ARSFI/HFSimulator/doc/QEX/attachments/Fig 1. Detailed block diagram of the IONOS Simulator.png

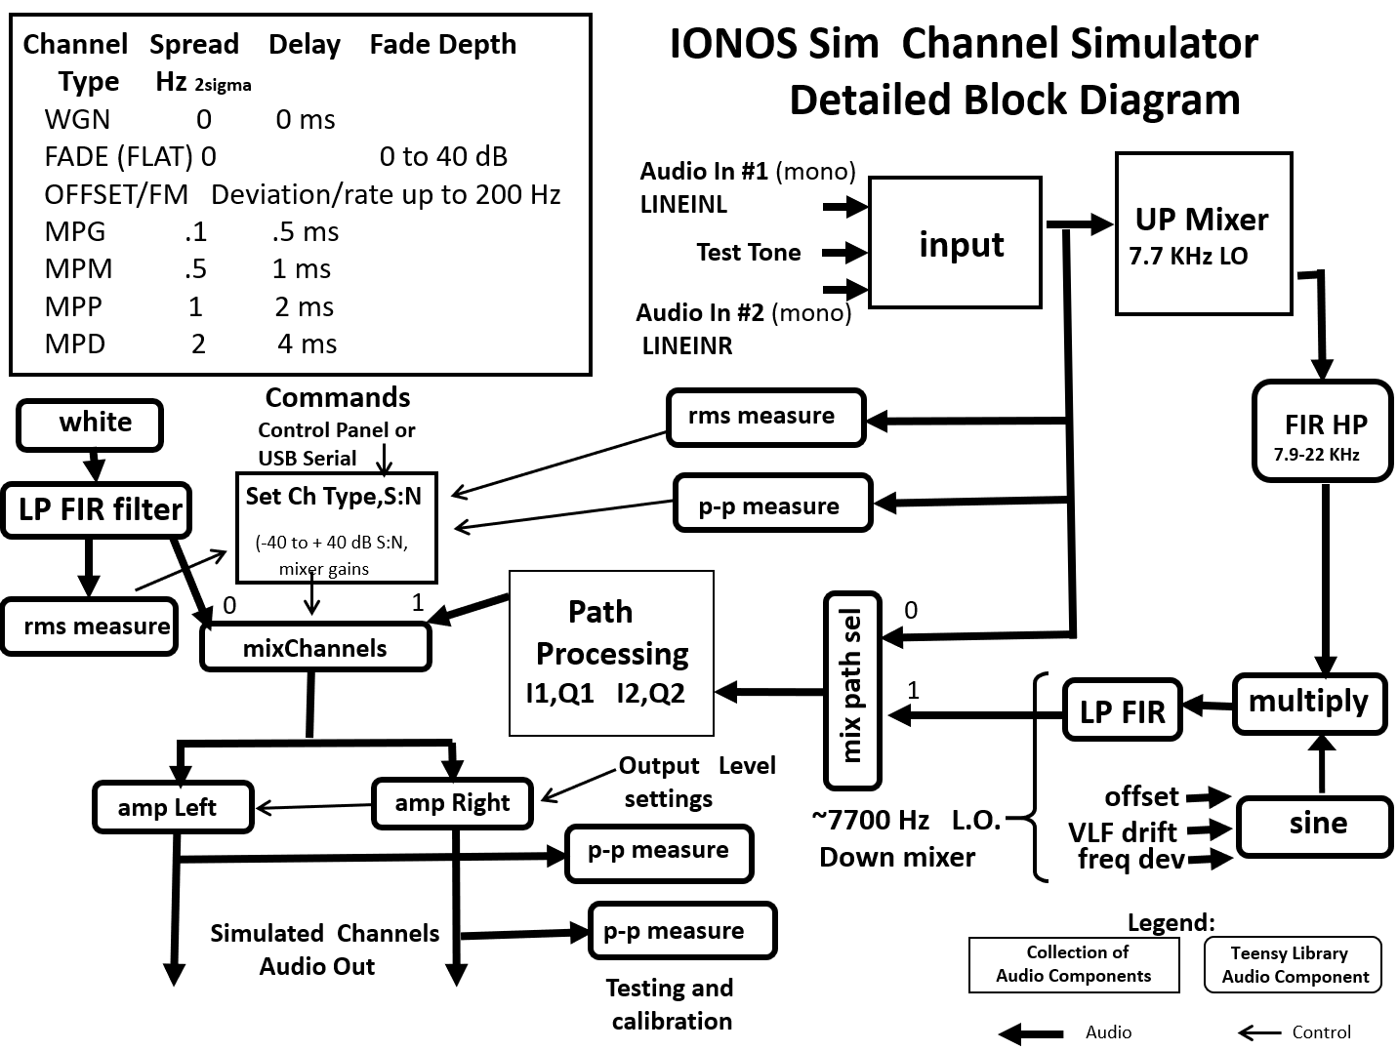
doc/QEX/attachments/Fig 1. Detailed block diagram of the IONOS Simulator.png
