ARSFI/HFSimulator/doc/QEX/attachments/Fig 3 Teensy 4.0 Processor and Audio Shield.png

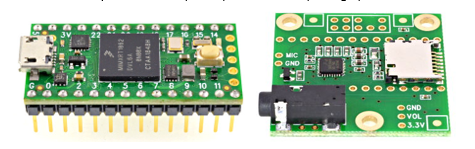
doc/QEX/attachments/Fig 3 Teensy 4.0 Processor and Audio Shield.png
