ARSFI/HFSimulator/doc/QEX/attachments/Fig 4 Photo of Rev 2 prototype PCB.png

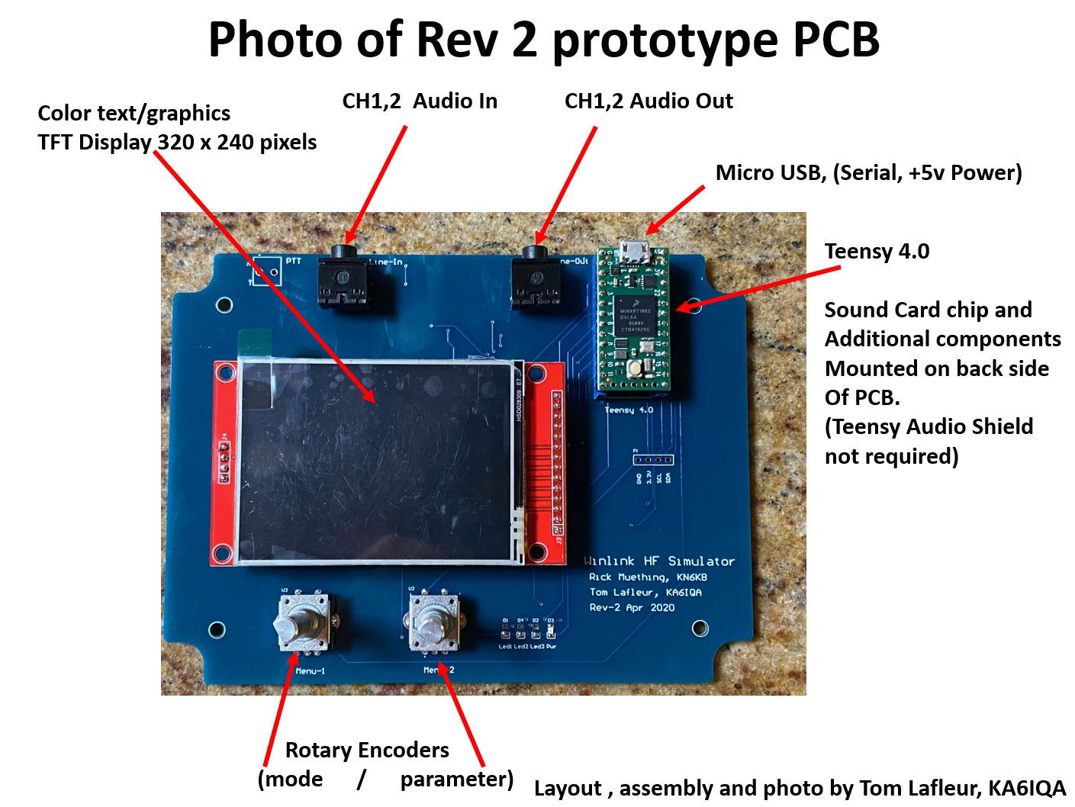
doc/QEX/attachments/Fig 4 Photo of Rev 2 prototype PCB.png
