ARSFI/HFSimulator/doc/QEX/attachments/Fig 8 Photo of First prototype production run with enclosure.png

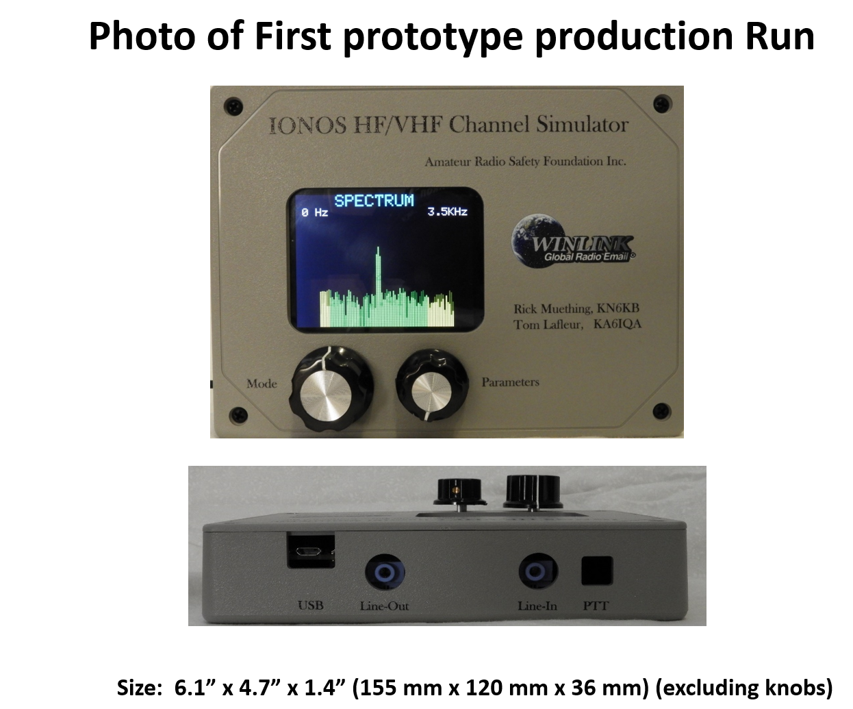
doc/QEX/attachments/Fig 8 Photo of First prototype production run with enclosure.png
