ARSFI/HFSimulator/doc/QEX/attachments/Fig 9 Gaussian 9 pole LP FIR Filter.png

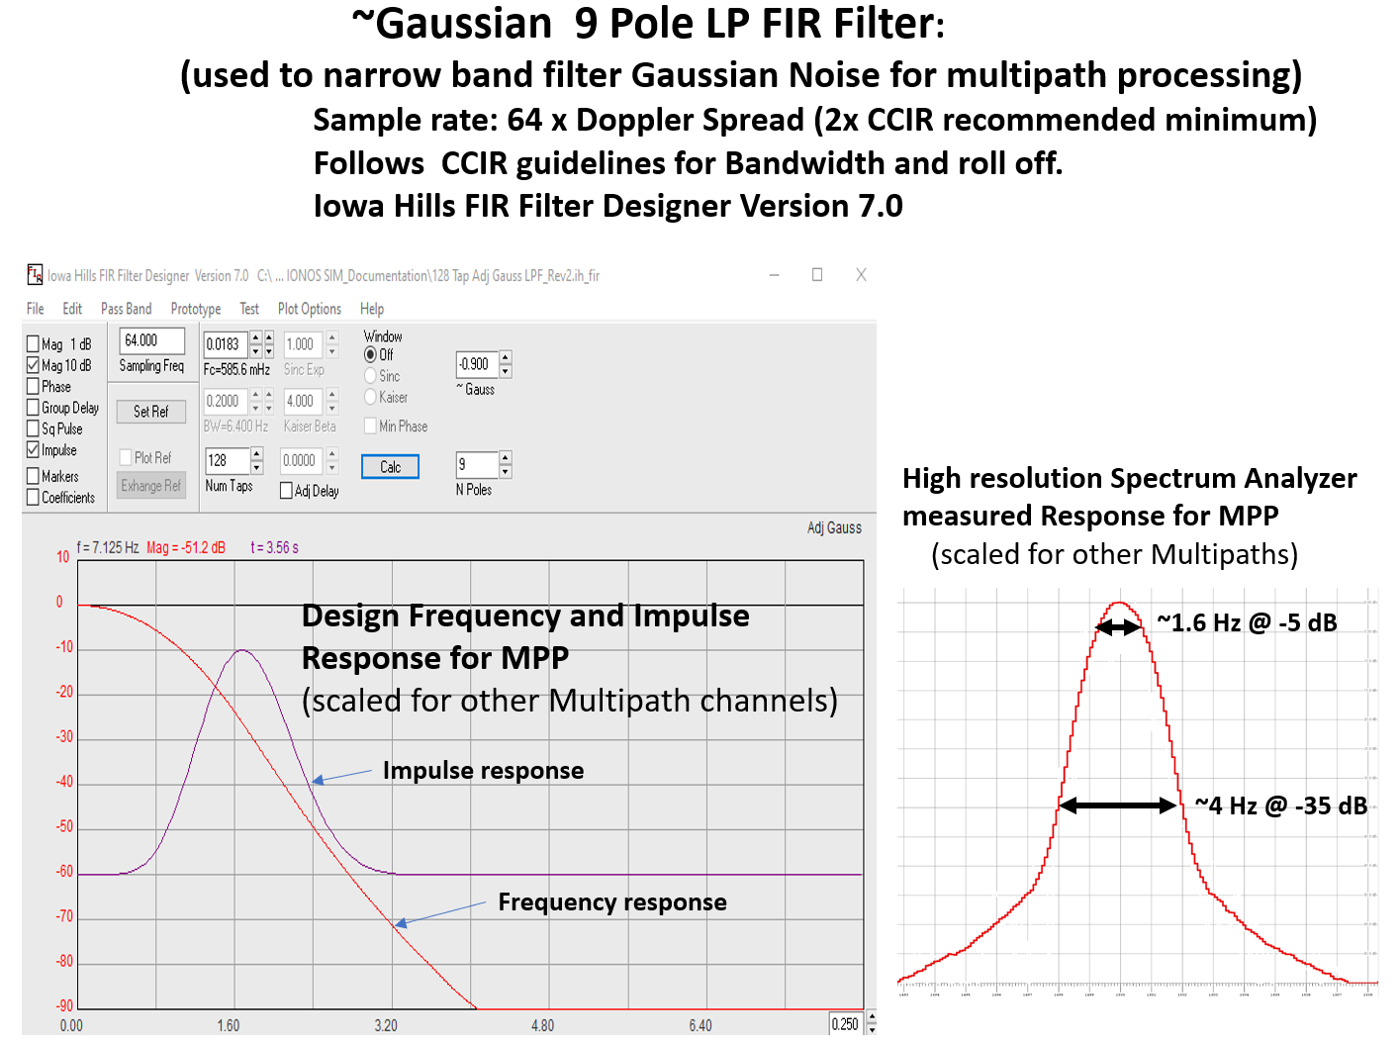
doc/QEX/attachments/Fig 9 Gaussian 9 pole LP FIR Filter.png
