ARSFI/HFSimulator/doc/QEX/attachments/Fig 10 Modem Connections to the IONOS Simulator for Half Duplex ARQ modeling.png

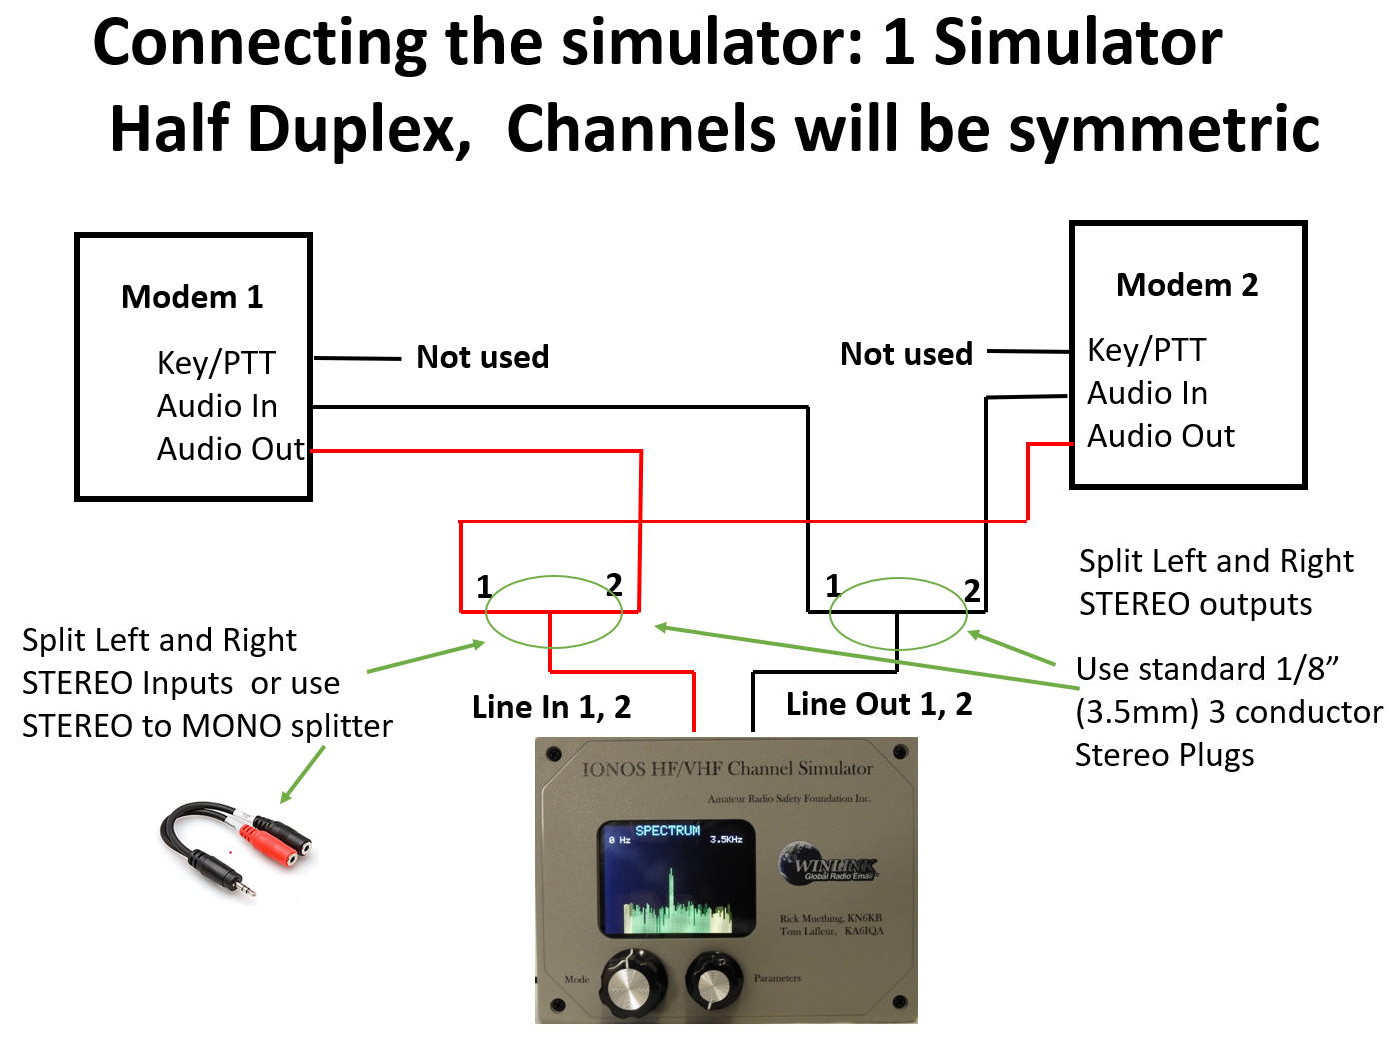
doc/QEX/attachments/Fig 10 Modem Connections to the IONOS Simulator for Half Duplex ARQ modeling.png
