ARSFI/HFSimulator/photos/IMG_9686.jpg

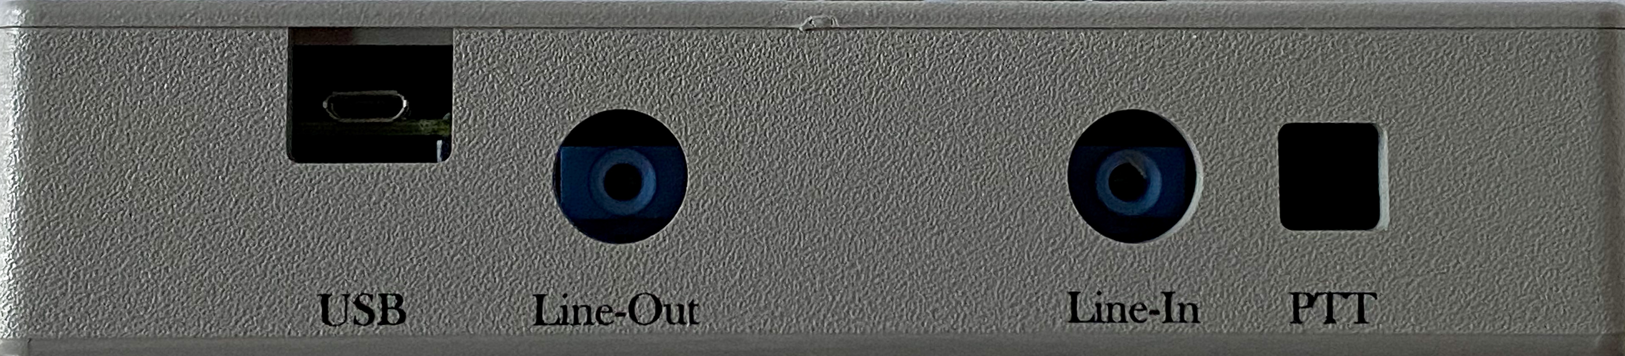
photos/IMG_9686.jpg
