ARSFI/HFSimulator/photos/IMG_9697.jpg

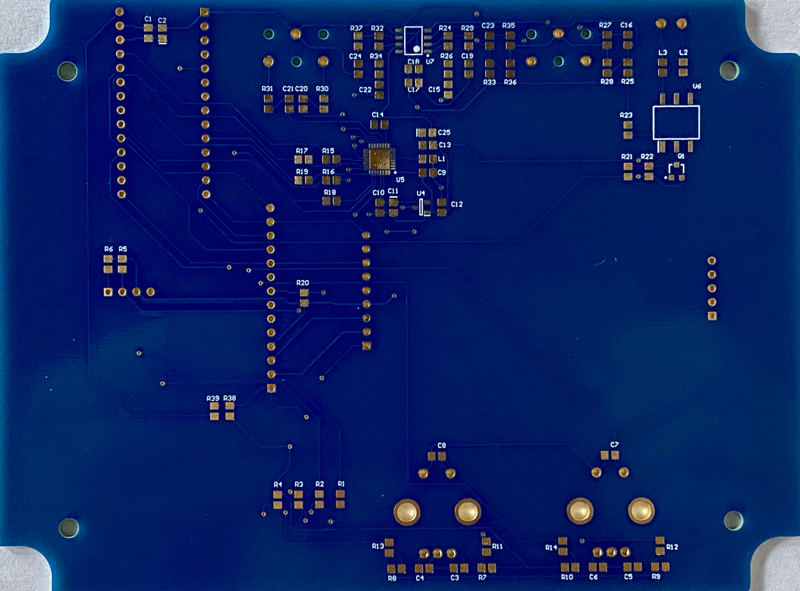
photos/IMG_9697.jpg
