ARSFI/HFSimulator/photos/IMG_9700.jpg

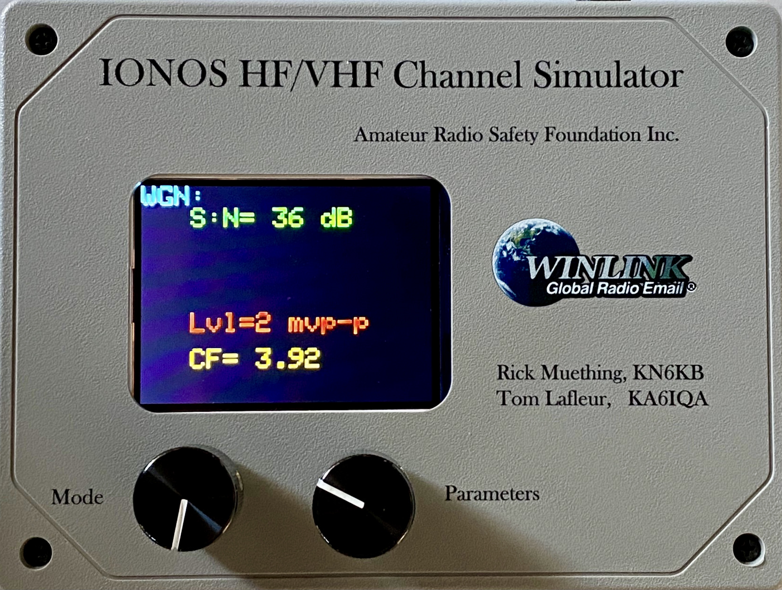
photos/IMG_9700.jpg
