ARSFI/HFSimulator/photos/IMG_9702.jpg

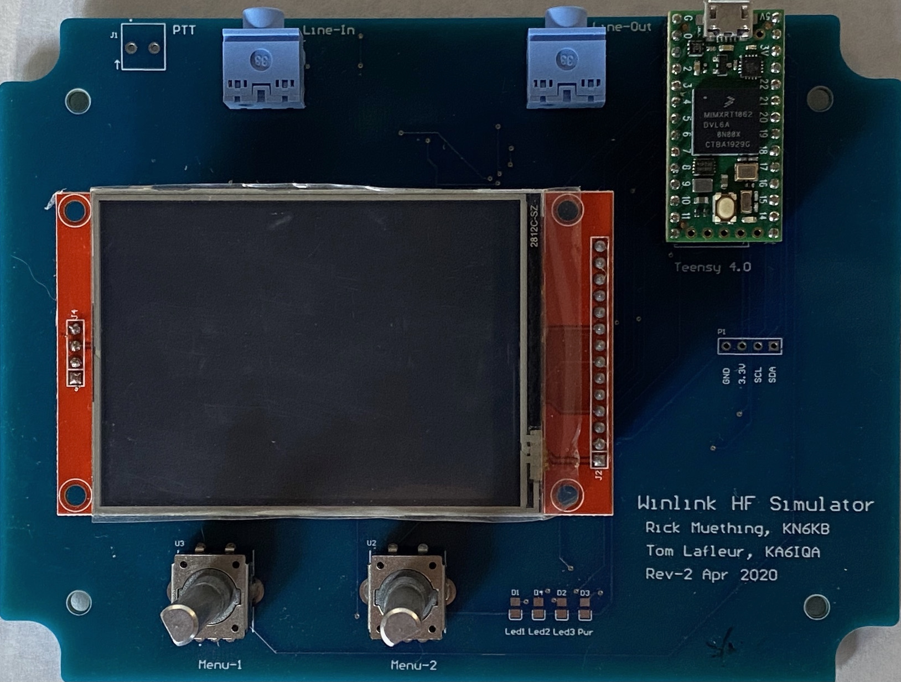
photos/IMG_9702.jpg
