ARSFI/HFSimulator/photos/IMG_9705.jpg

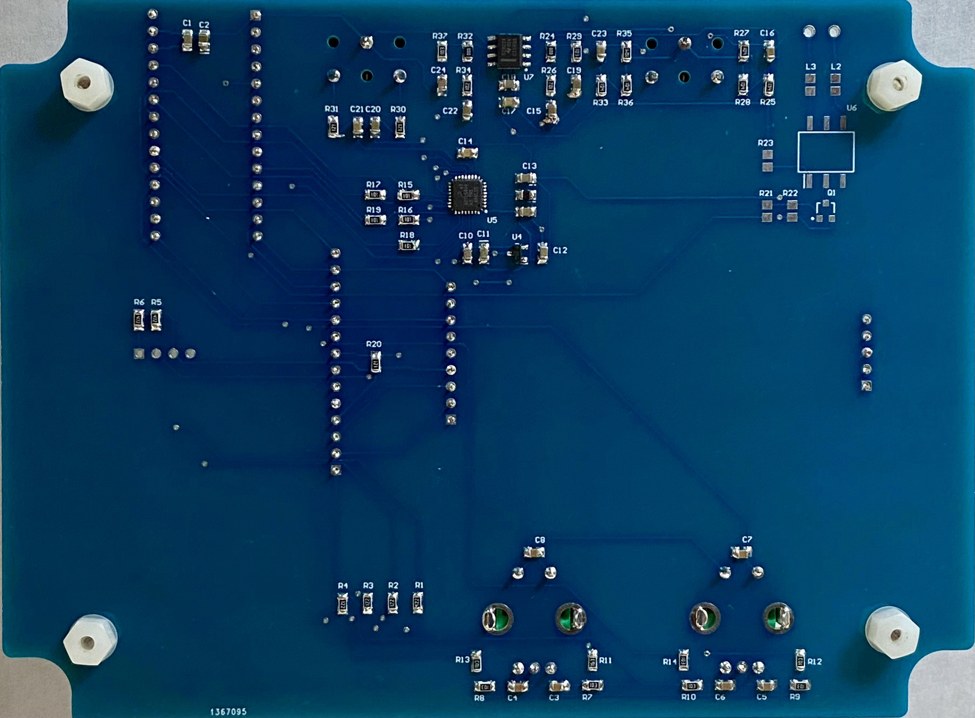
photos/IMG_9705.jpg
