ARSFI/HFSimulator/photos/IMG_9708.jpg

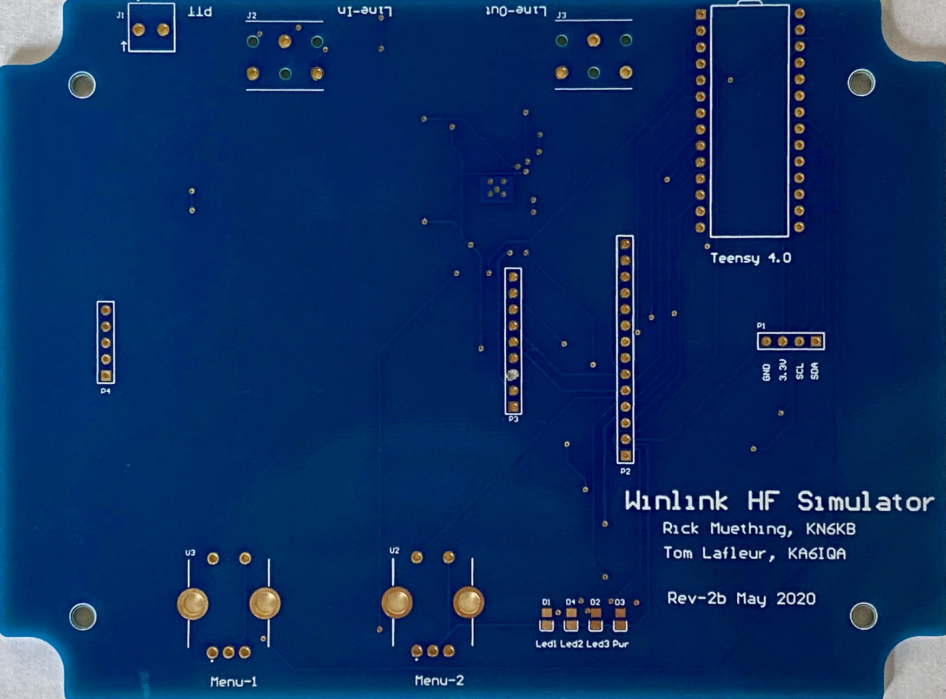
photos/IMG_9708.jpg
