ARSFI/HFSimulator/doc/QEX/attachments/Fig 11 Performance verses S_N for 5 ARQ Protocols White Gaussian Noise.png

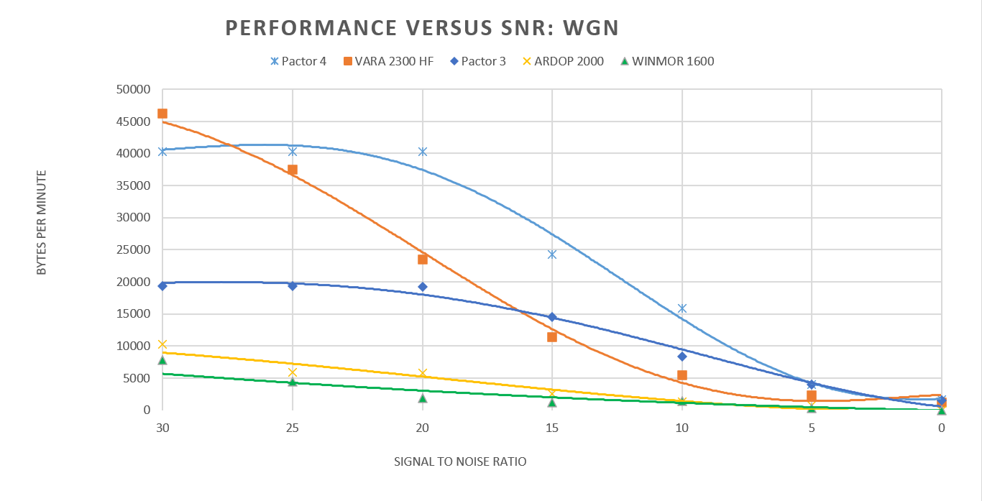
doc/QEX/attachments/Fig 11 Performance verses S_N for 5 ARQ Protocols White Gaussian Noise.png
