ARSFI/HFSimulator/doc/QEX/attachments/Fig 13 Performance verses S_N for 5 ARQ Protocols Multipath Poor MPP.png

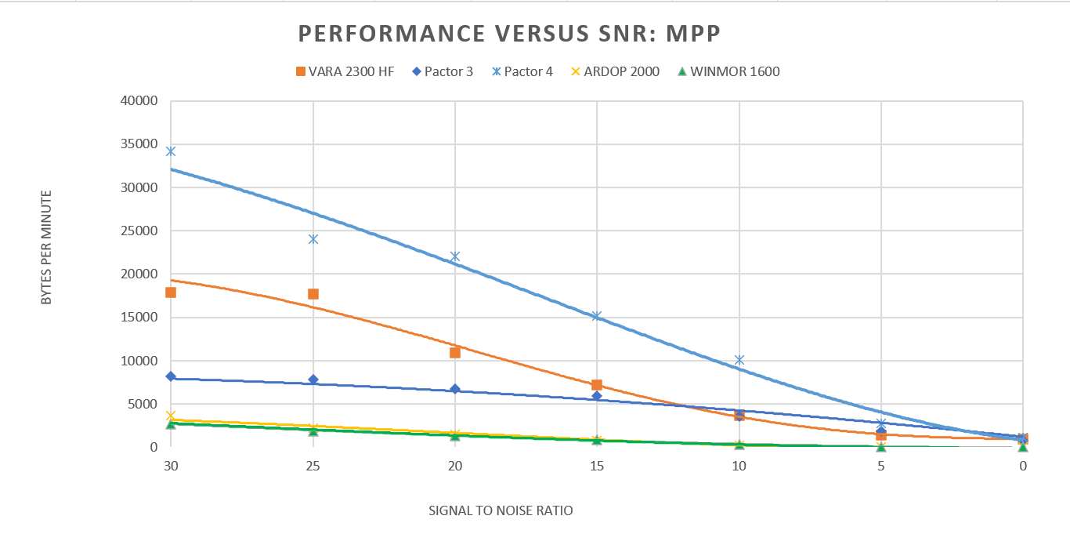
doc/QEX/attachments/Fig 13 Performance verses S_N for 5 ARQ Protocols Multipath Poor MPP.png
