ARSFI/HFSimulator/doc/QEX/attachments/Fig 14 Performance for VARA FM and AX.25_FX.25 Packet.png

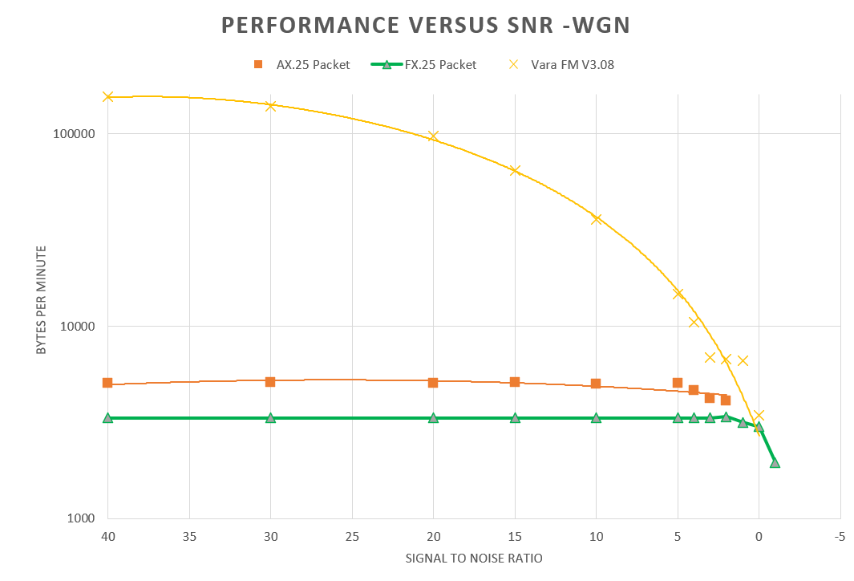
doc/QEX/attachments/Fig 14 Performance for VARA FM and AX.25_FX.25 Packet.png
