ARSFI/HFSimulator/hardware/Ver 2/sch/HF-Simulator Rev-2b.pdf

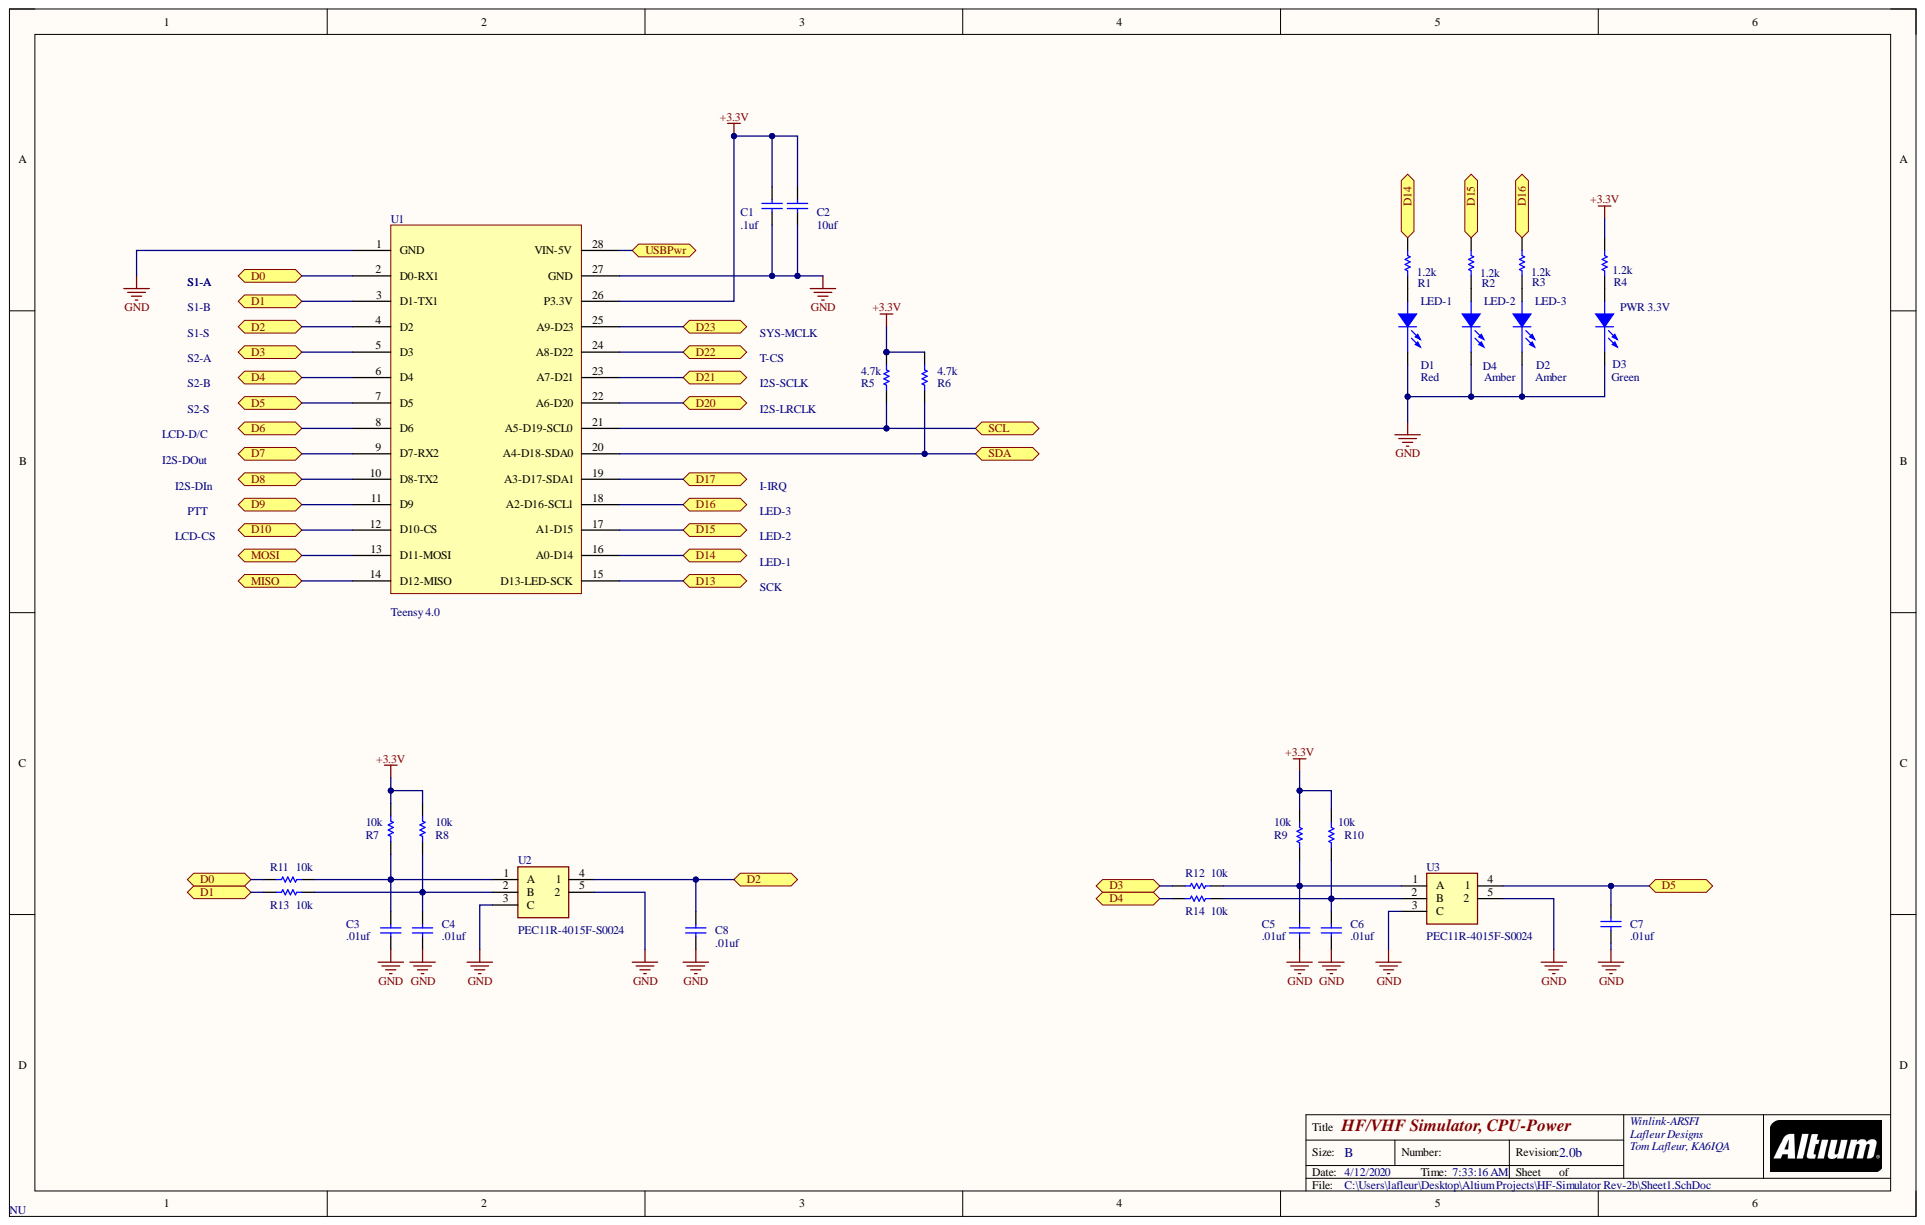
[picture p107: page 1]

Title HF/VHF Simulator, CPU-Power | Winlink-ARSFI Lafleur Designs Tom Lafleur, KA6IQA

Size: B | Number: | Revision: 2.0b
Date: 4/12/2020 Time: 7:33:16 AM | | Sheet of

C:\Users\lafleur\Desktop\AltiumProjects\HF-Simulator Rev-2b\Sheet1.SchDoc

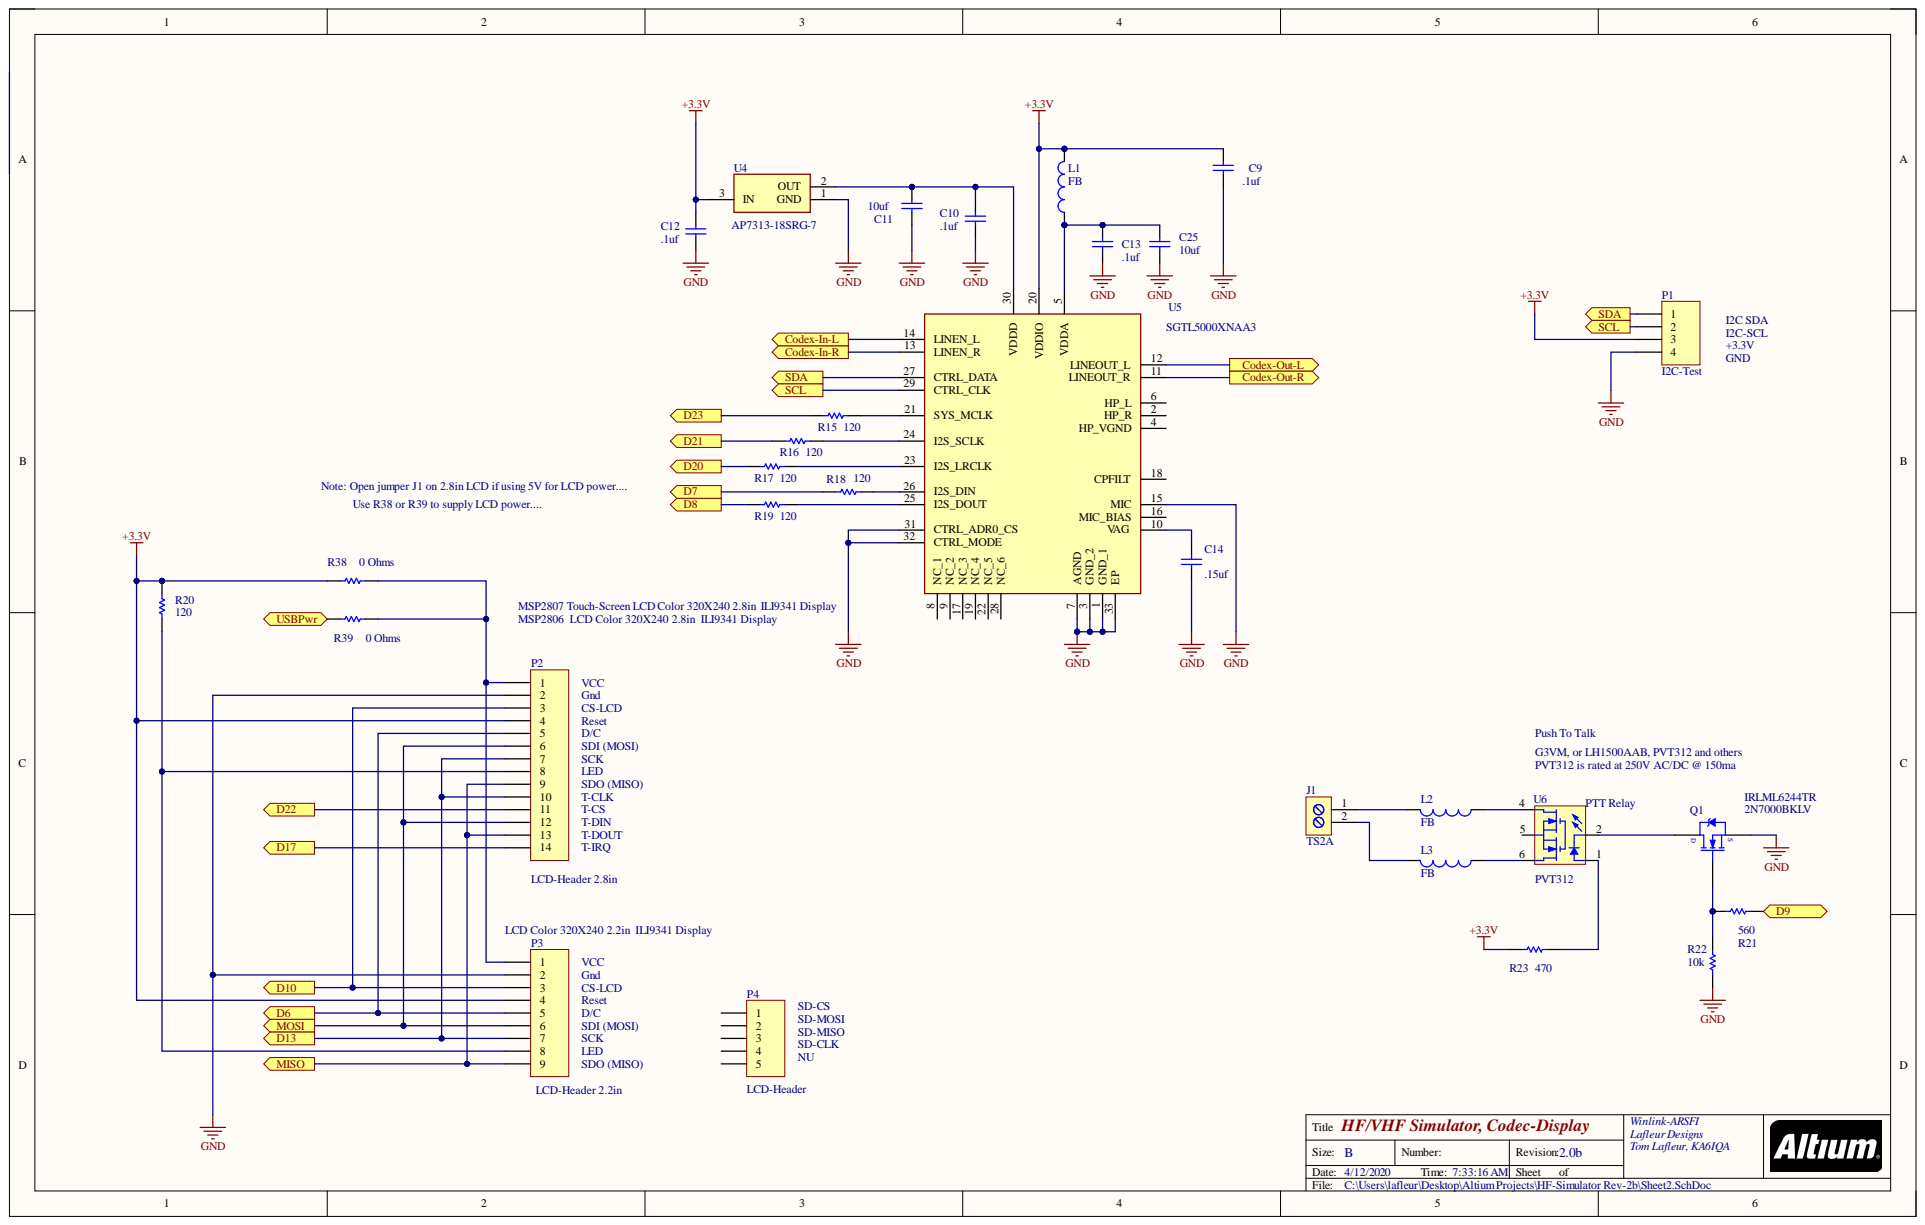
[picture p108: page 2]

Note: Open jumper J1 on 2.8in LCD if using 5V for LCD power....
Use R38 or R39 to supply LCD power....

R38 0 Ohms

MSP2807 Touch-Screen LCD Color 320X240 2.8in ILI9341 Display
MSP2806 LCD Color 320X240 2.8in ILI9341 Display

R39 0 Ohms

Push To Talk
G3VM, or LH1500AAB, PVT312 and others
PVT312 is rated at 250V AC/DC @ 150ma

HF/VHF Simulator, Codec-Display
Title

C:\Users\lafleur\Desktop\AltiumProjects\HF-Simulator Rev-2b\Sheet2.SchDoc

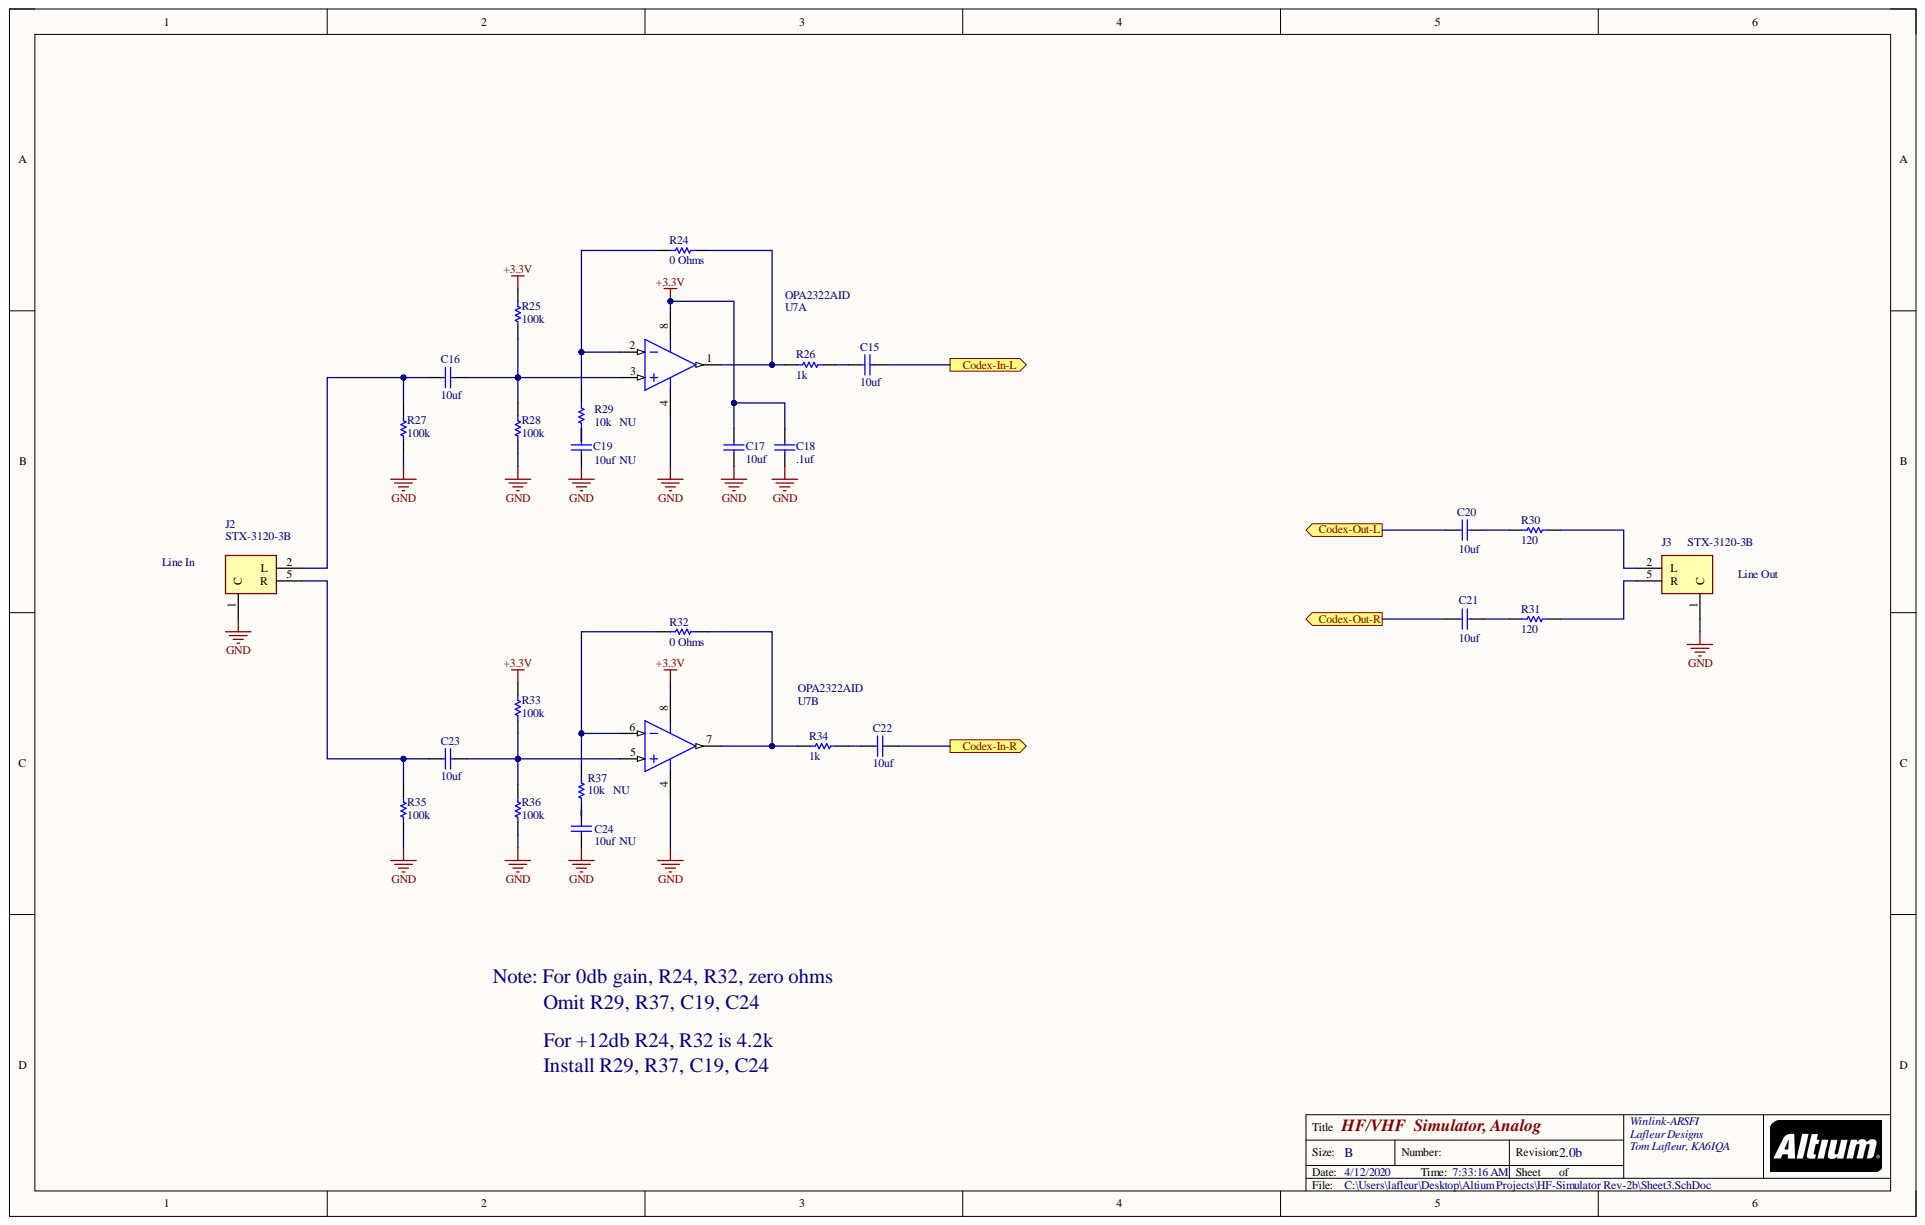
[picture p109: page 3]

Ti tl e HF/VHF Simulato r, Analo g | Winl ink-ARSFI Lafleur Des igns Tom Lafleur, KA6I QA

Si z e : B | N umber : | Revi s i on: 2 . 0 b
Dat e : 4/12/ 20 20 Ti me: 7:33:16 AM | | Sheet of

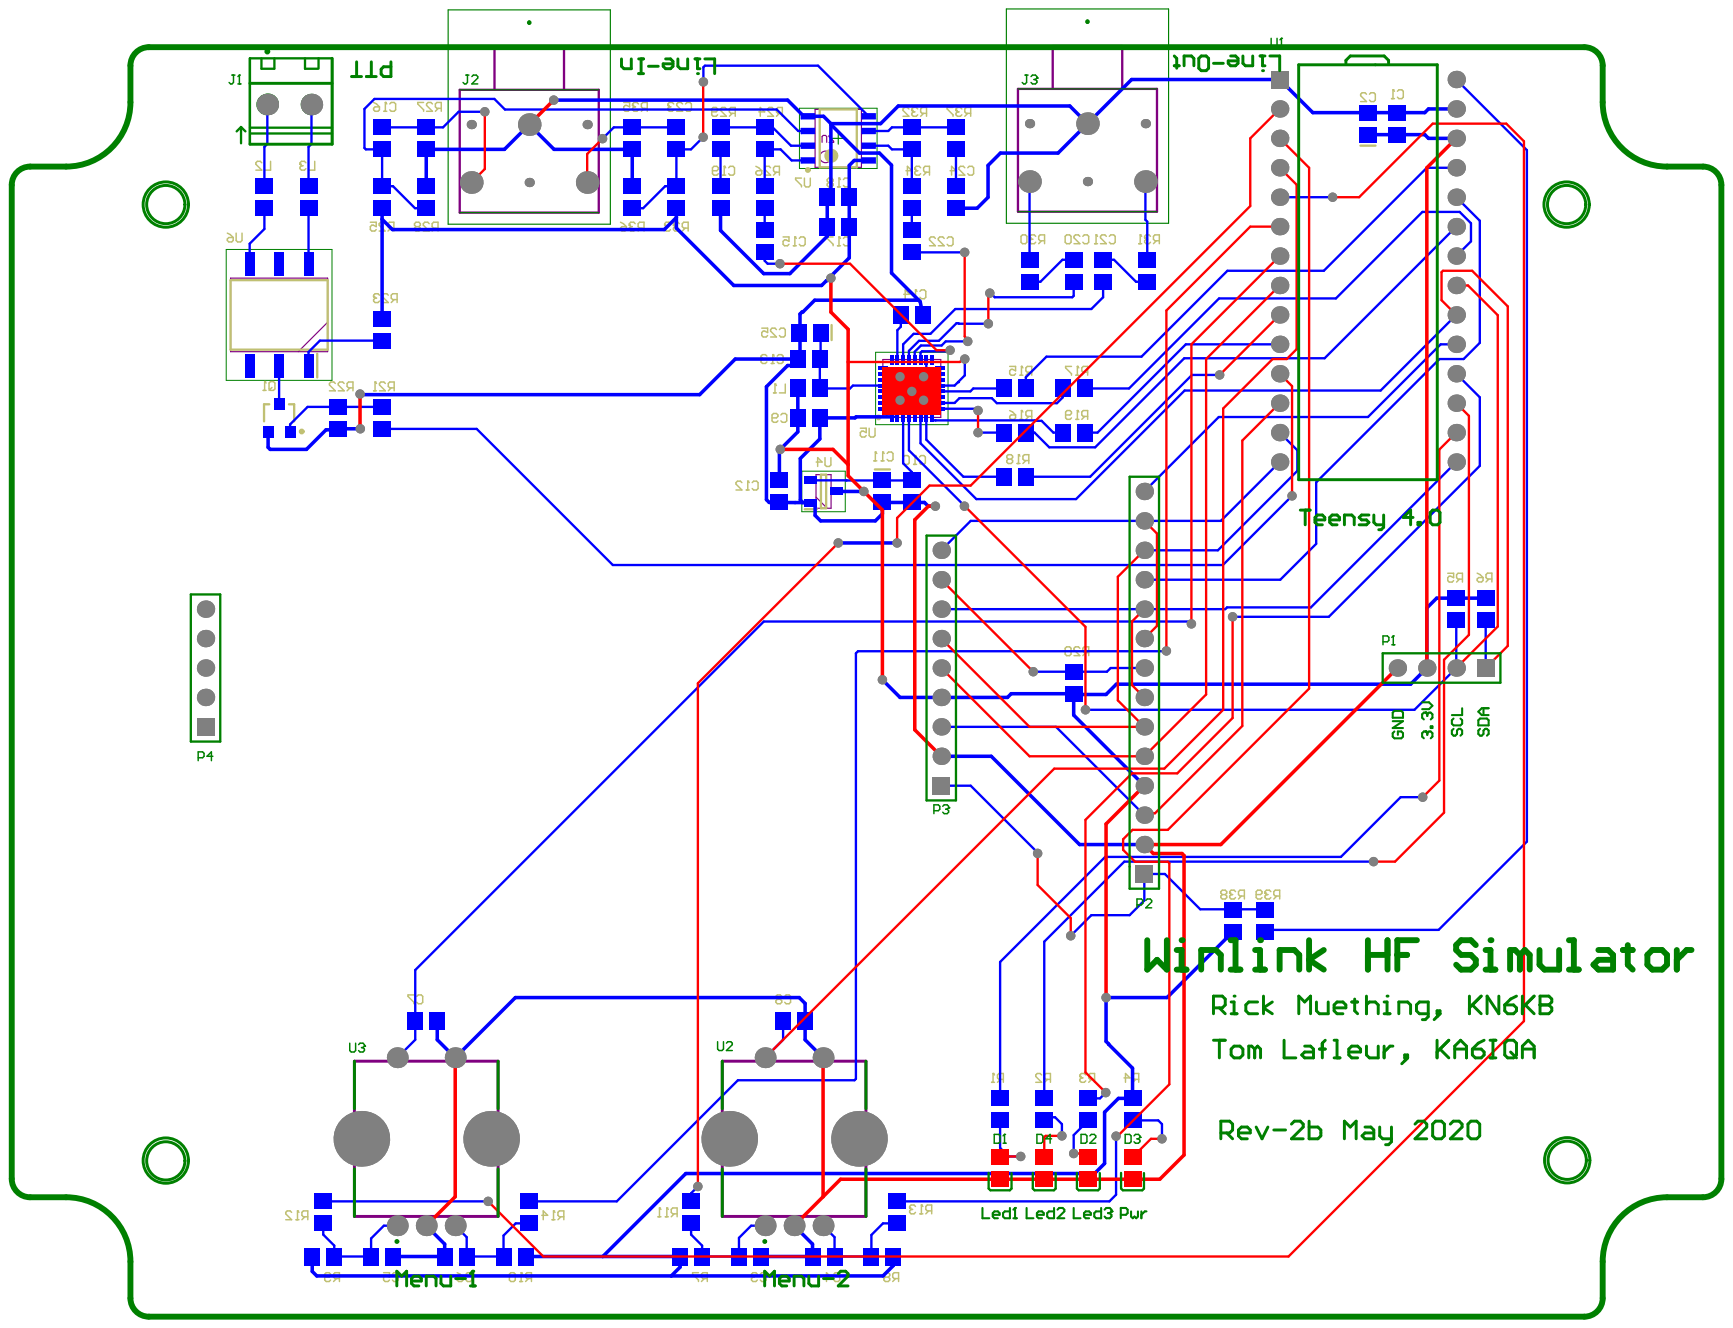
[picture p110: page 4]
