ARSFI/HFSimulator/hardware/Ver 2/sch/IONOS Simulator Schematic Sheet1.pdf

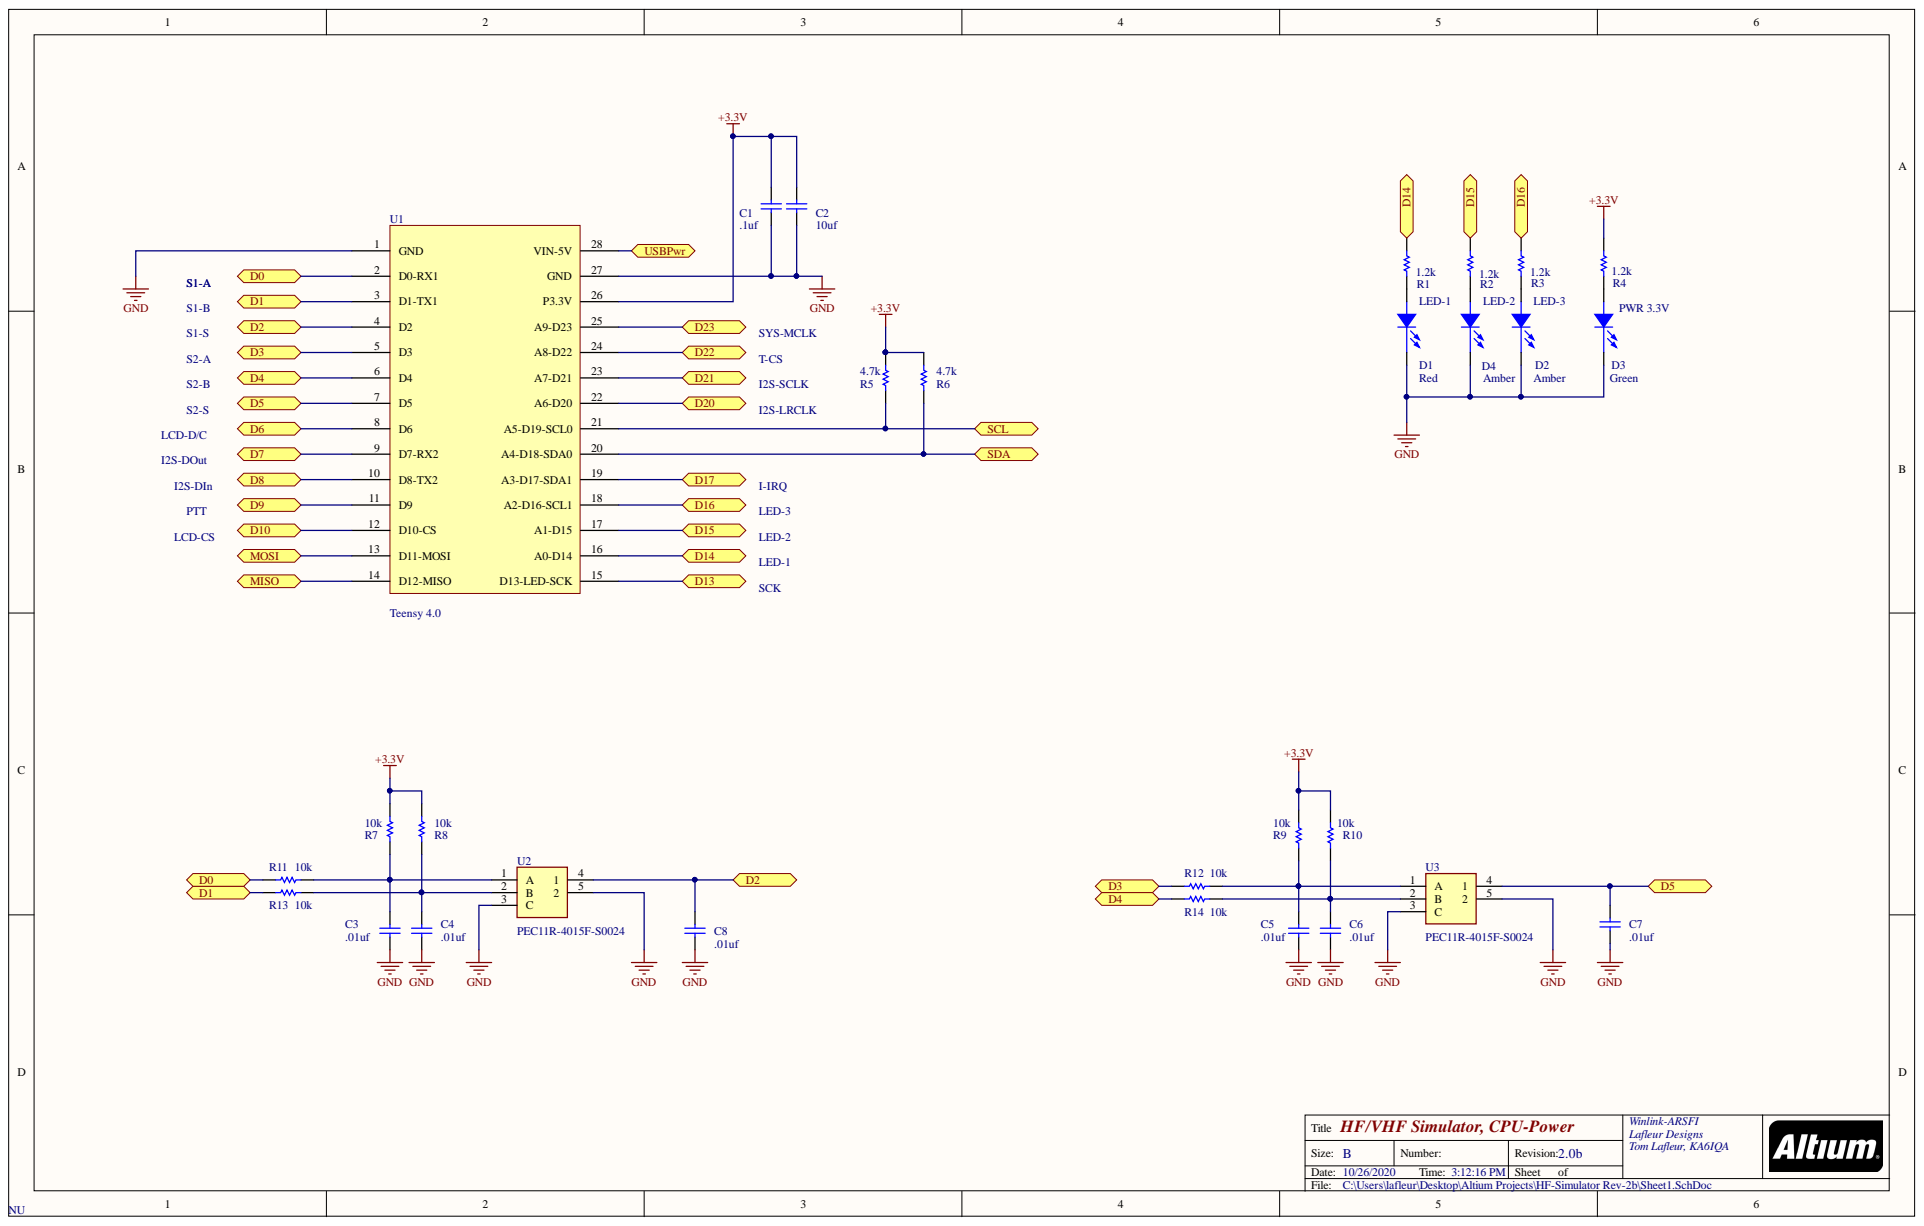
[picture p111: page 1]

HF/VHF Simulator, CPU-Power Title | Winlink-ARSFI Lafleur Designs Tom Lafleur, KA6IQA

Size: B | Number: | Revision: 2.0b
Date: 10/26/2020 Time: 3:12:16 PM | | Sheet of
File: C:\Users\lafleur\Desktop\Altium Projects\HF-Simulator Rev-2b\Sheet1.SchDoc
