ARSFI/HFSimulator/hardware/Ver 2/sch/IONOS Simulator Schematic Sheet3.pdf

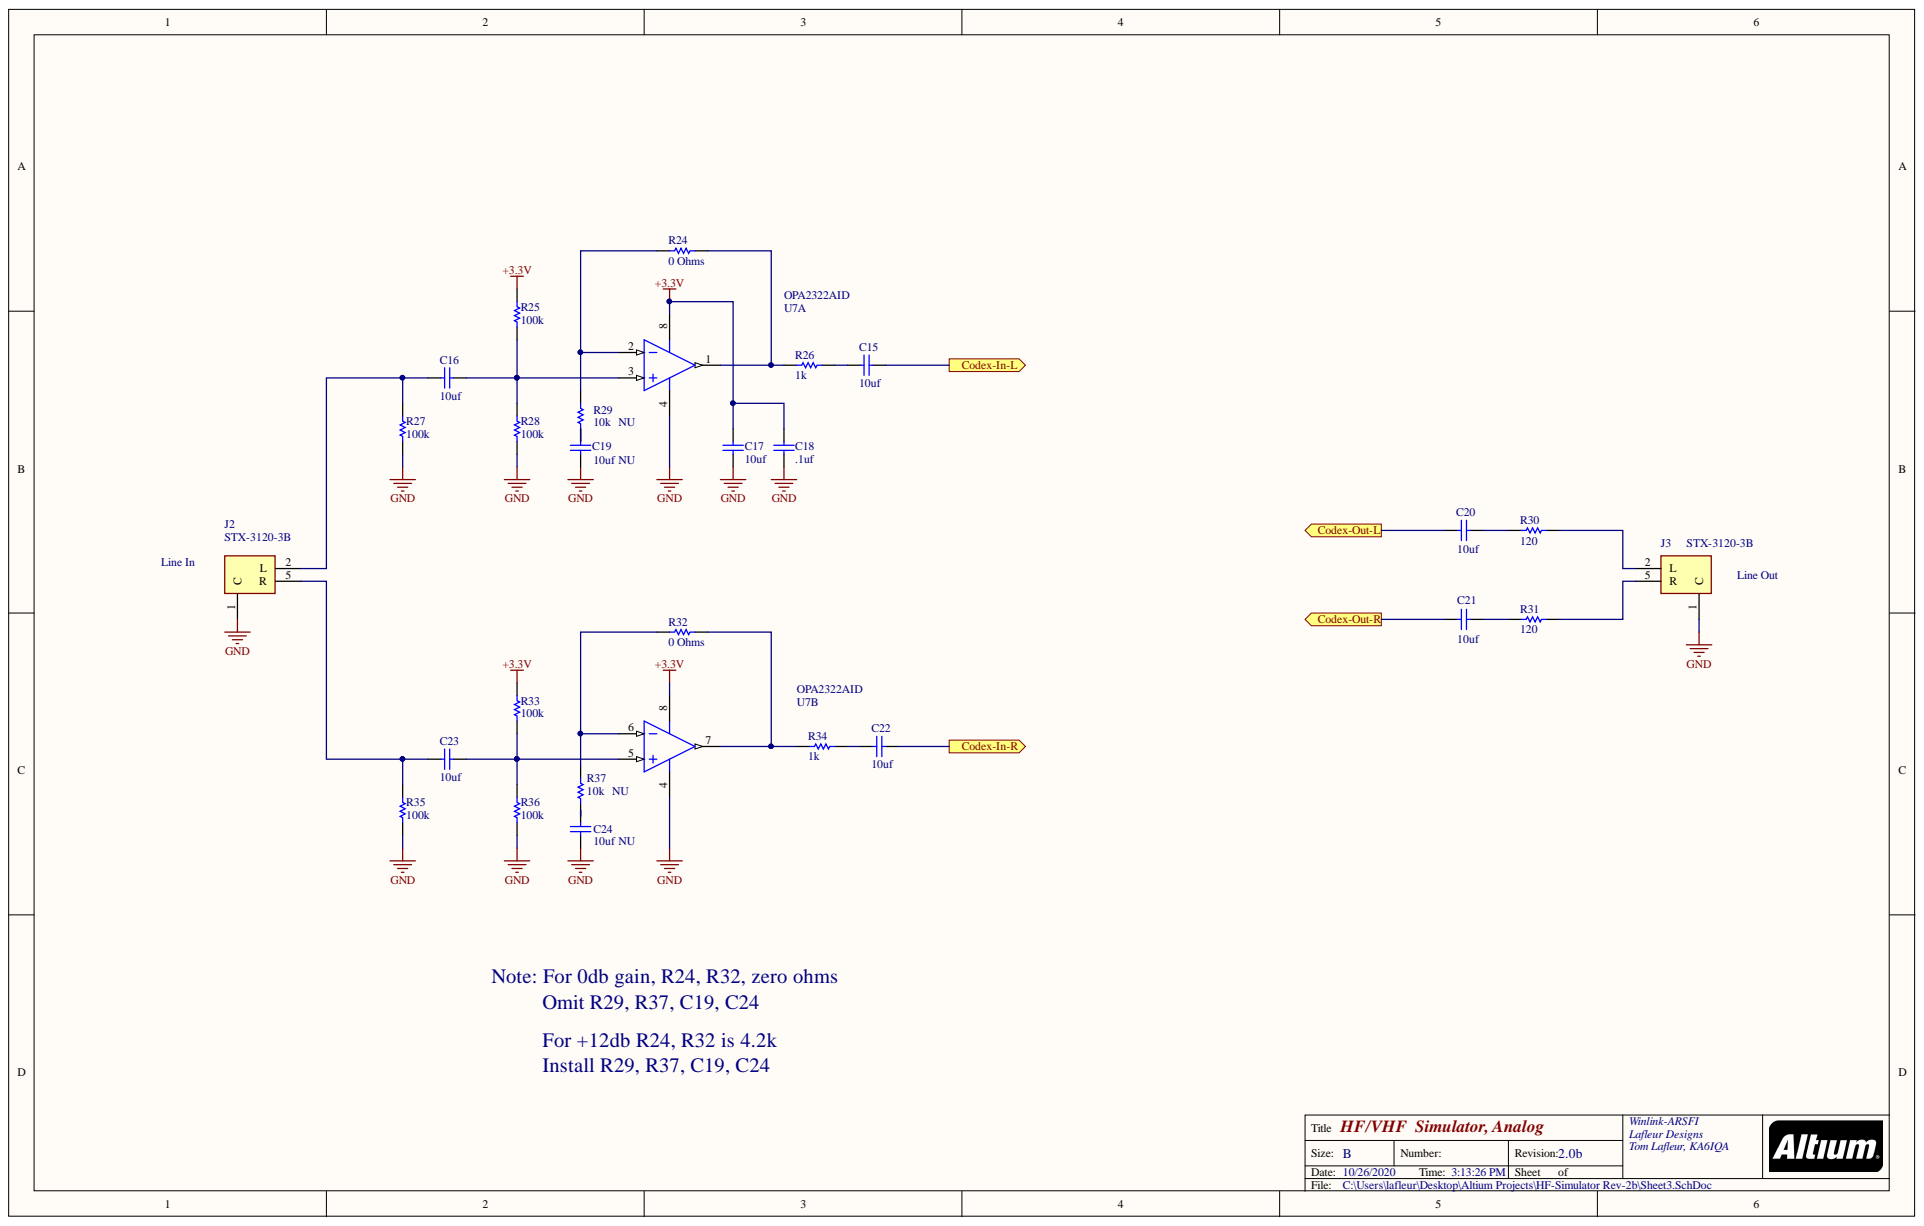
[picture p112: page 1]

HF/VHF Simulato r, Analo g Ti tl e | Winl ink-A RSFI Lafleur Des igns Tom Lafleur, KA6I QA

Size: B | Number : | Revi s ion: 2 . 0 b
Date: Ti me: | | Sheet of
Fi le: s \HF-Si mulator Rev-2b\Sheet3.SchDoc
