ARSFI/HFSimulator/hardware/Ver 3/case/PolyCase Ver-3/HF-Sim PolyCase V3/Rev-2/DC-45PMBYT_ASS'Y_BOX _BodyDrawing v1.pdf

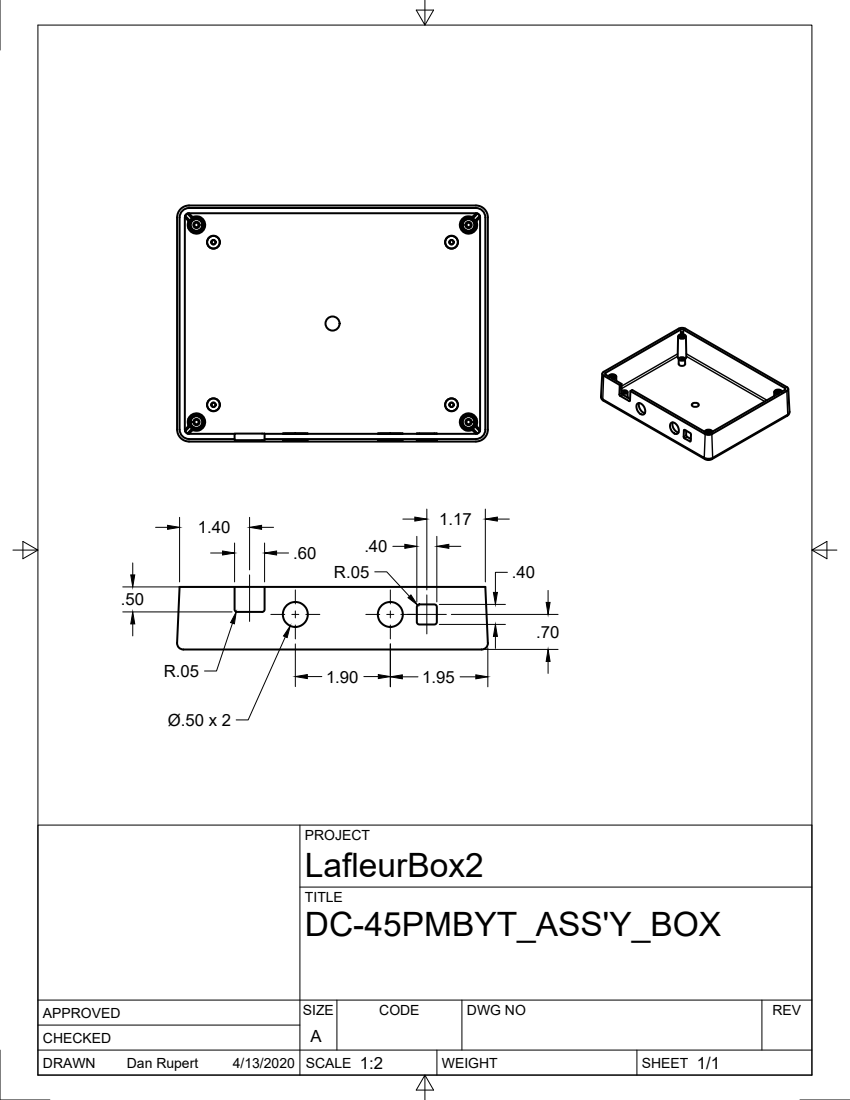
[picture p113: page 1]
SIZE; CODE; DWG NO; REV; Dan Rupert
