ARSFI/HFSimulator/hardware/Ver 3/case/PolyCase Ver-3/HF-Sim PolyCase V3/Rev-2/DC-45PMBYT_ASS'Y_BOX Drawing LID v1.pdf

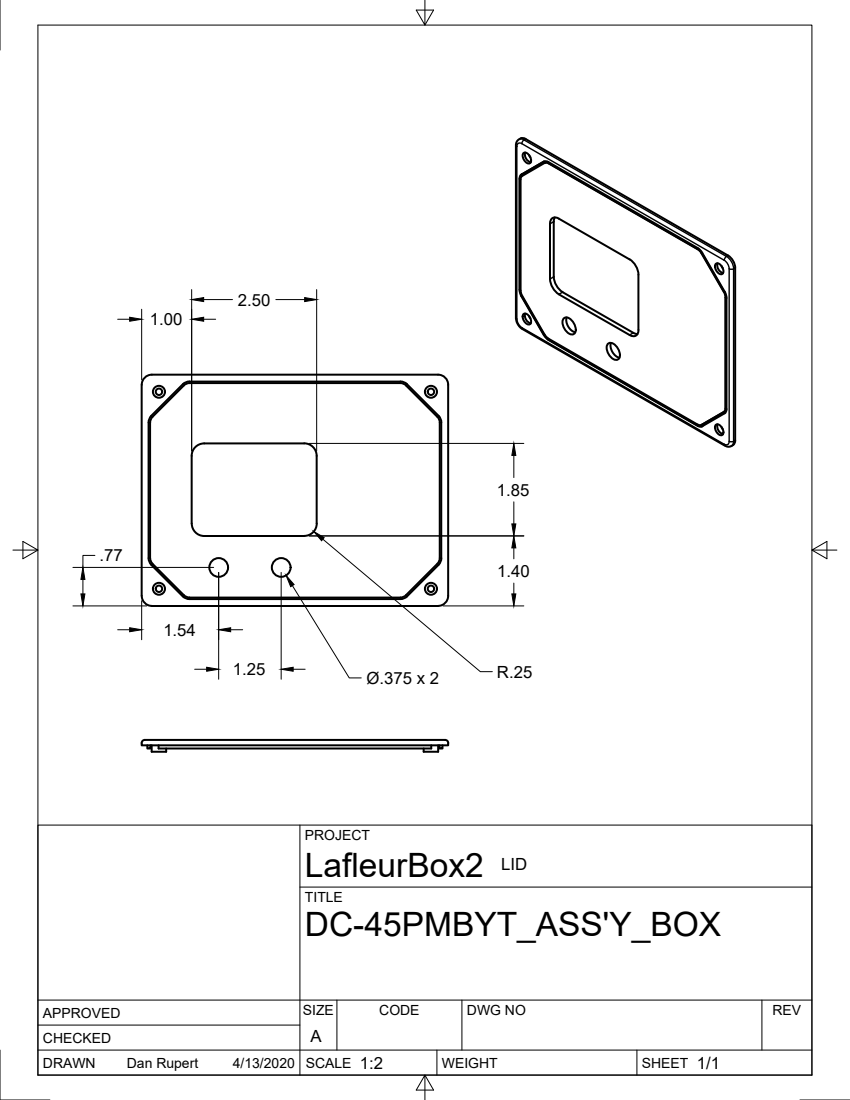
[picture p114: page 1]
SIZE; CODE; DWG NO; REV; Dan Rupert
