ARSFI/HFSimulator/hardware/Ver 3/case/PolyCase Ver-3/HF-Sim PolyCase V3/Rev-1/Lafleur_DC-45PMBYT_ASS'Y Drawing v1 LID.pdf

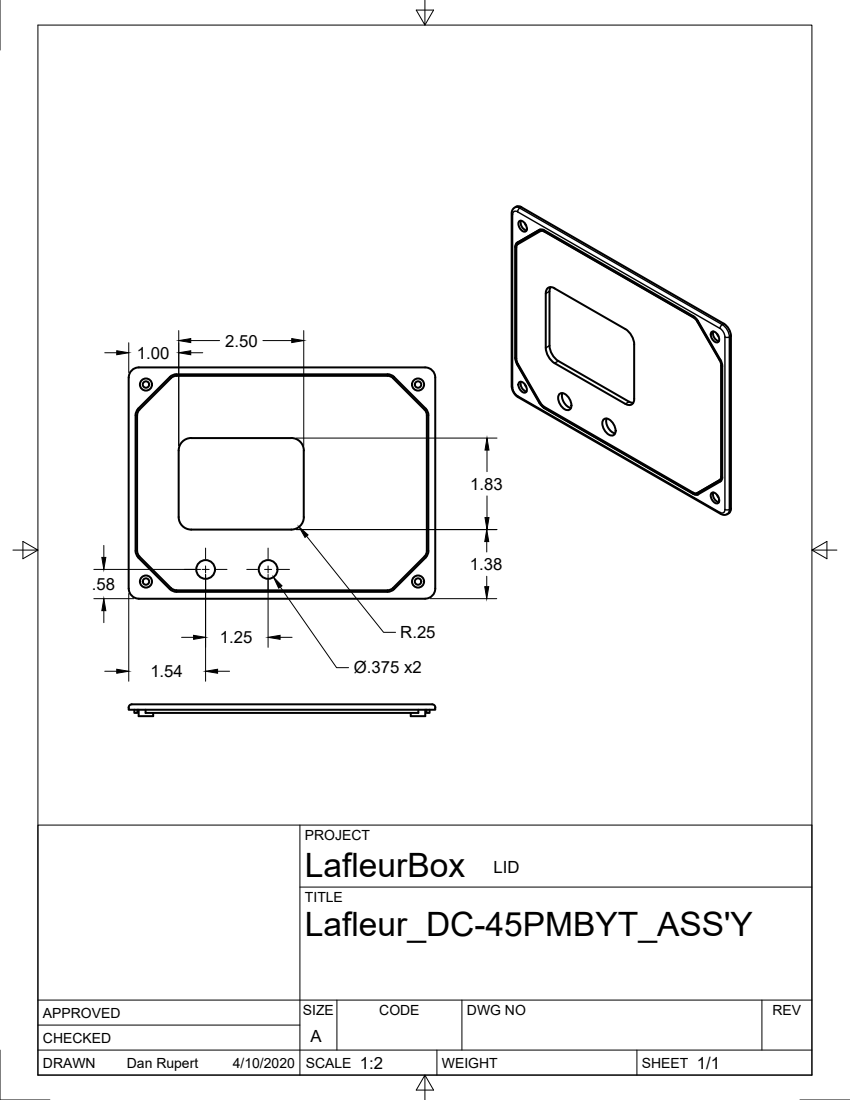
[picture p115: page 1]
SIZE; CODE; DWG NO; REV; Dan Rupert
