ARSFI/HFSimulator/hardware/Ver 3/case/PolyCase Ver-3/HF-Sim PolyCase V3/Rev-1/Lafleur_DC-45PMBYT_Box Drawing v1.pdf

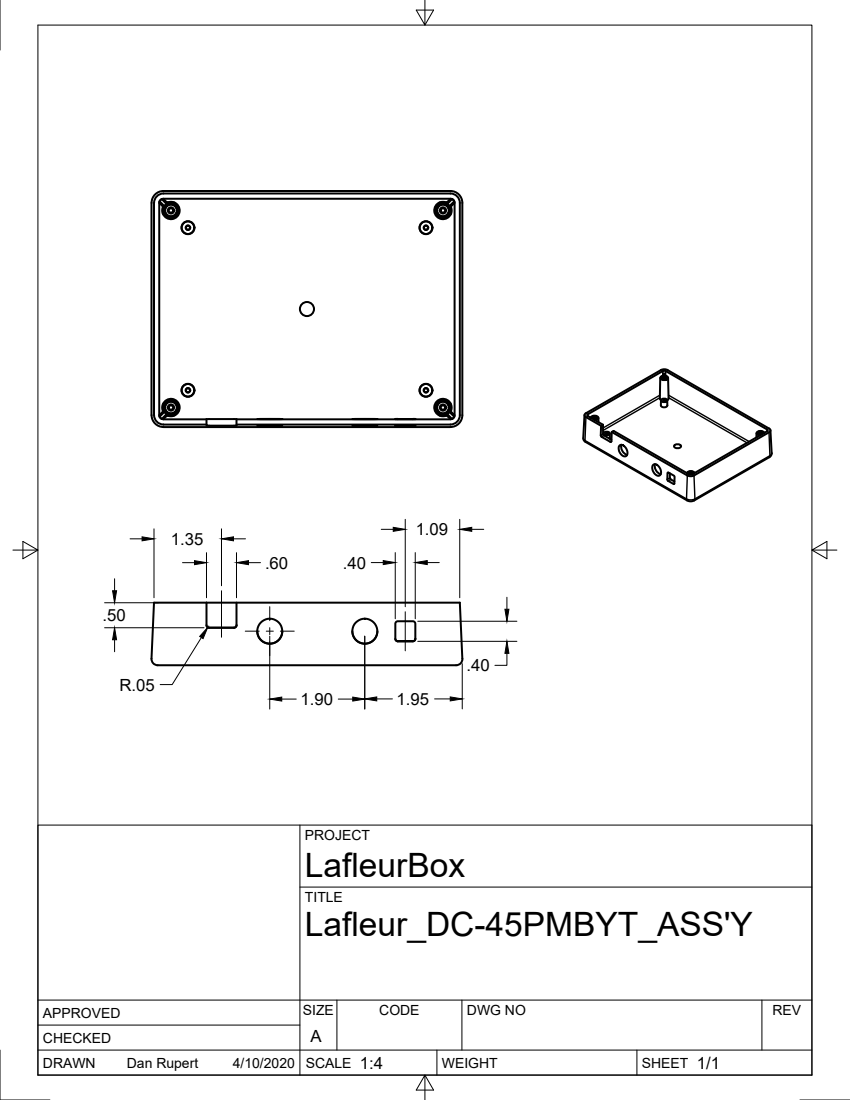
[picture p116: page 1]
SIZE; CODE; DWG NO; REV; Dan Rupert
